sledepus/Development-of-a-Distributed-Synchronized-Camera-System-for-Real-Time-Underwater-Monitoring/Mechanical Assembly - CAD/Hexadome Prototype/Lens_asm.SLDASM

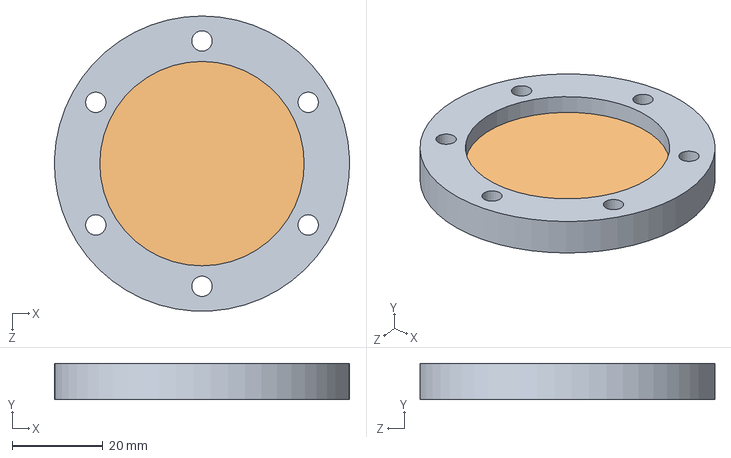
[picture p4: CAD file, 2025-05-22]
Mechanical Assembly - CAD/Hexadome Prototype/Lens_asm.SLDASM
65.0 x 8.00 x 64.9 mm
Lens_glass_45
Lens_cover_simple
