sledepus/Development-of-a-Distributed-Synchronized-Camera-System-for-Real-Time-Underwater-Monitoring/Mechanical Assembly - CAD/Hexadome Prototype/Wide_node_case_asm.SLDASM

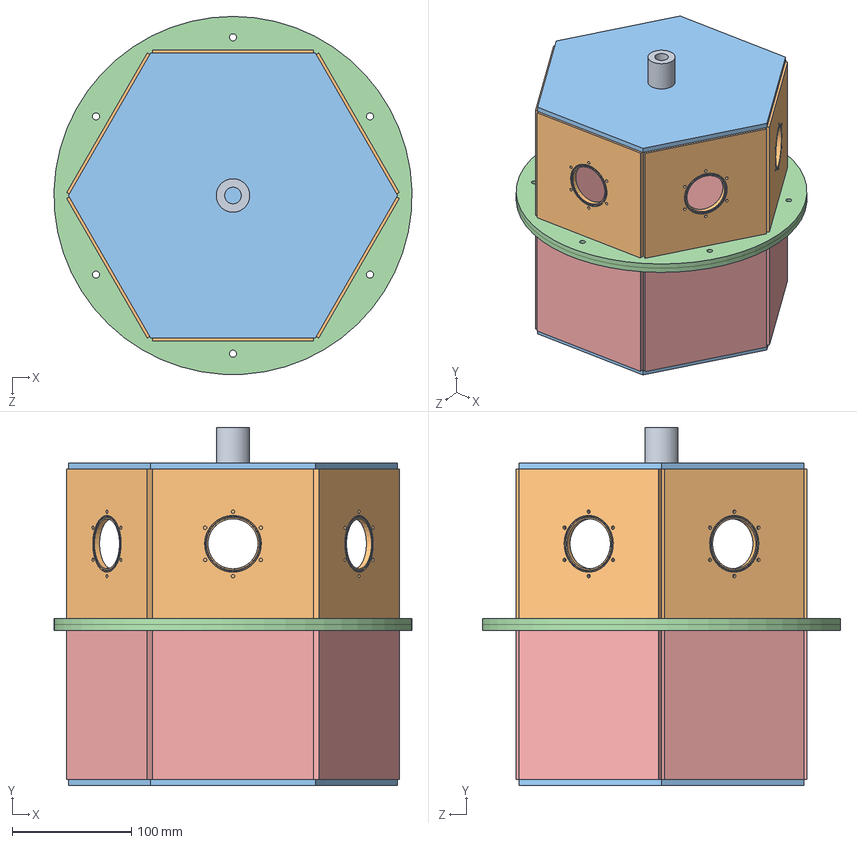
[picture p5: CAD file, 2025-05-22]
Mechanical Assembly - CAD/Hexadome Prototype/Wide_node_case_asm.SLDASM
299.9 x 300.0 x 300.0 mm
Wide_bottom_wall x 6
Wide_flange x 2
Wide_lock x 2
Wide_top_wall x 6
Boss
