sledepus/Development-of-a-Distributed-Synchronized-Camera-System-for-Real-Time-Underwater-Monitoring/Mechanical Assembly - CAD/Hexadome Prototype/Wide_bottom_asm.SLDASM

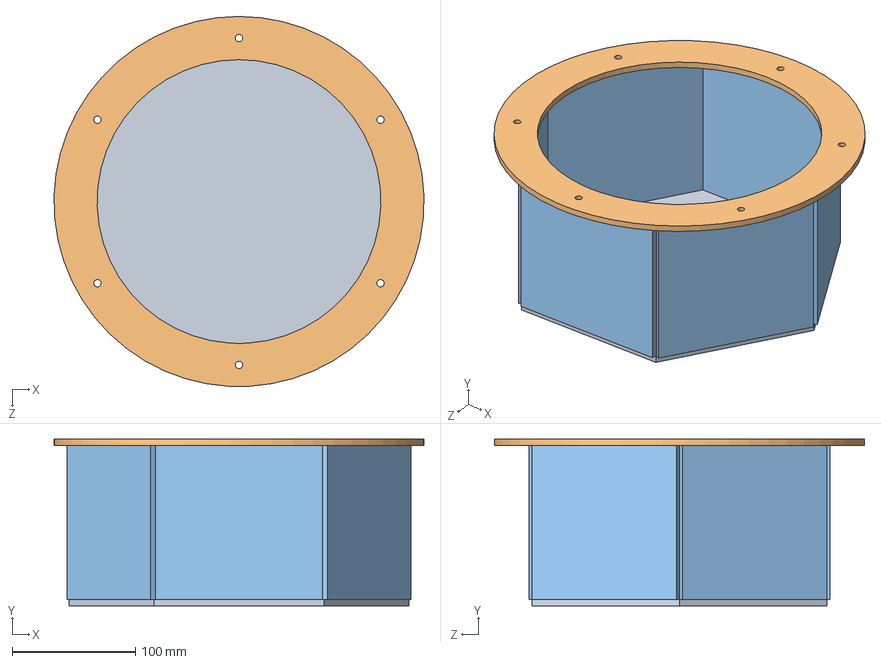
[picture p6: CAD file, 2025-05-22]
Mechanical Assembly - CAD/Hexadome Prototype/Wide_bottom_asm.SLDASM
299.9 x 135.0 x 300.0 mm
Wide_bottom_wall x 6
Wide_flange
Wide_lock
