sledepus/Development-of-a-Distributed-Synchronized-Camera-System-for-Real-Time-Underwater-Monitoring/Mechanical Assembly - CAD/Hexadome Prototype/Jetson_Dummy_Serial_board.SLDPRT

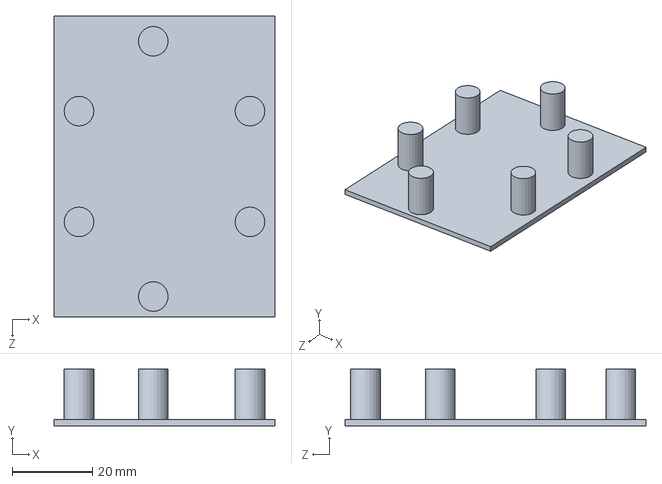
[picture p14: CAD file, 2025-05-22]
Mechanical Assembly - CAD/Hexadome Prototype/Jetson_Dummy_Serial_board.SLDPRT
55.0 x 14.1 x 75.0 mm
