sledepus/Development-of-a-Distributed-Synchronized-Camera-System-for-Real-Time-Underwater-Monitoring/Mechanical Assembly - CAD/Sensor Board/Large_Sensor_PCB_bracket.SLDPRT

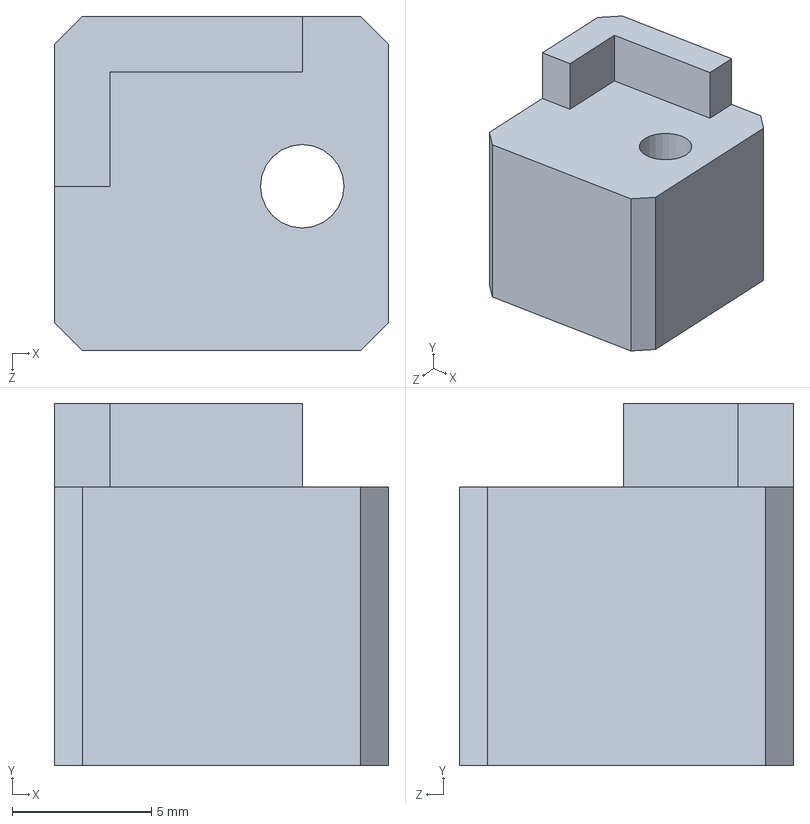
[picture p15: CAD file, 2025-05-22]
Mechanical Assembly - CAD/Sensor Board/Large_Sensor_PCB_bracket.SLDPRT
12.0 x 13.0 x 12.0 mm
