sledepus/Development-of-a-Distributed-Synchronized-Camera-System-for-Real-Time-Underwater-Monitoring/Electronics/Power board/local symbols/EEV-FK2A221M.stp

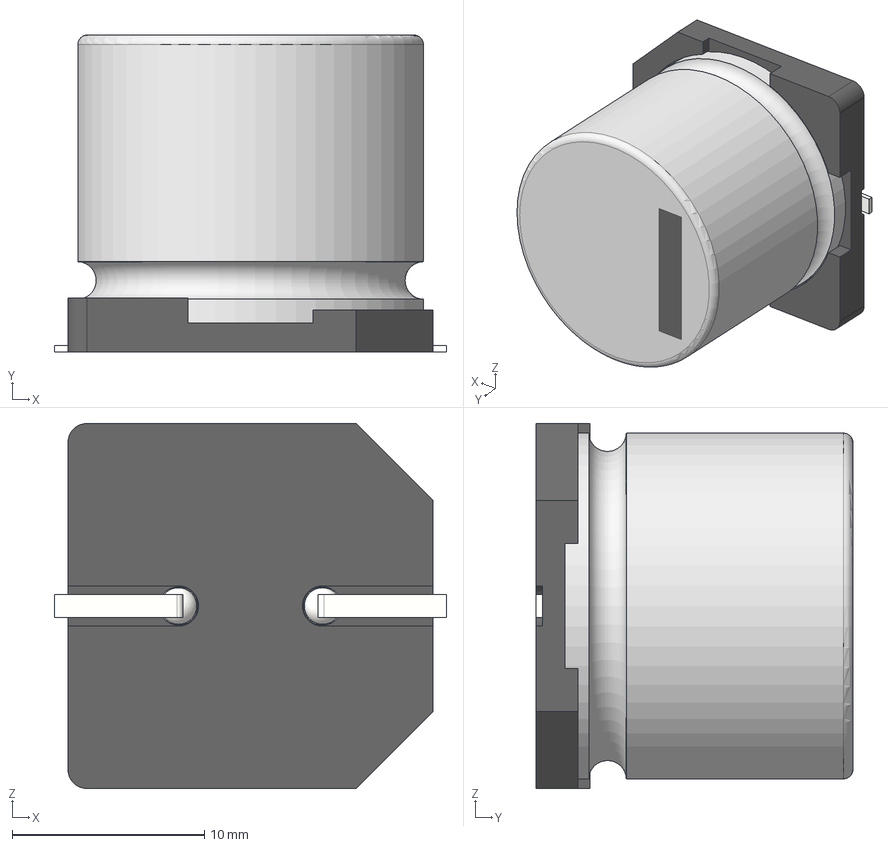
[picture p16: CAD file, 2025-05-22]
Electronics/Power board/local symbols/EEV-FK2A221M.stp
20.4 x 16.5 x 19.0 mm
標準品ケースΦ18x15L SIDE CODE K1 6
標準品座版Φ18 SIZE CODE K16
標準品リード線Φ18 SIZE CODE K1 6 x 2
