sledepus/Development-of-a-Distributed-Synchronized-Camera-System-for-Real-Time-Underwater-Monitoring/Mechanical Assembly - CAD/Final updated design/Bottom_node.SLDPRT

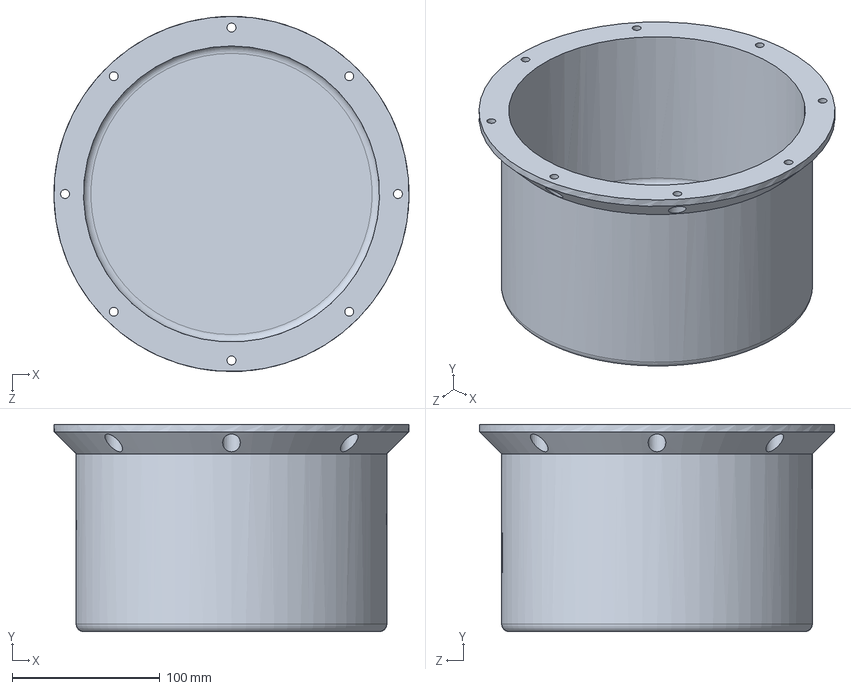
[picture p17: CAD file, 2025-05-22]
Mechanical Assembly - CAD/Final updated design/Bottom_node.SLDPRT
239.9 x 140.0 x 240.0 mm
