sledepus/Development-of-a-Distributed-Synchronized-Camera-System-for-Real-Time-Underwater-Monitoring/Mechanical Assembly - CAD/Final updated design/Hook.SLDPRT

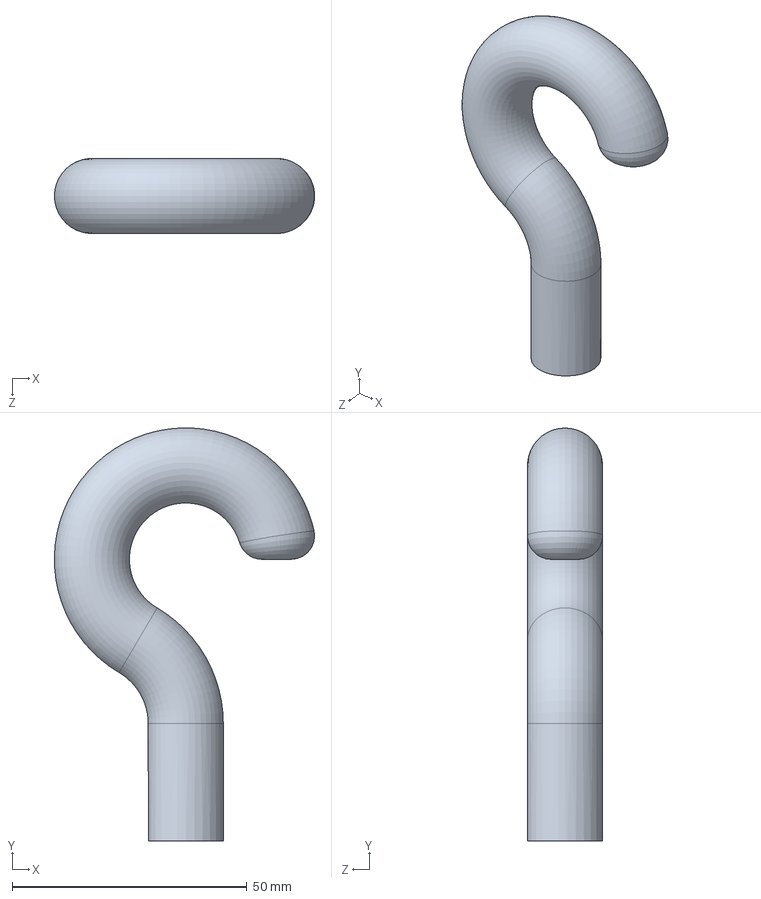
[picture p18: CAD file, 2025-05-22]
Mechanical Assembly - CAD/Final updated design/Hook.SLDPRT
55.4 x 88.0 x 16.0 mm
