sledepus/Development-of-a-Distributed-Synchronized-Camera-System-for-Real-Time-Underwater-Monitoring/Electronics/Power board/local symbols/Download_STP_WE-XHMI-1090 (rev1).stp

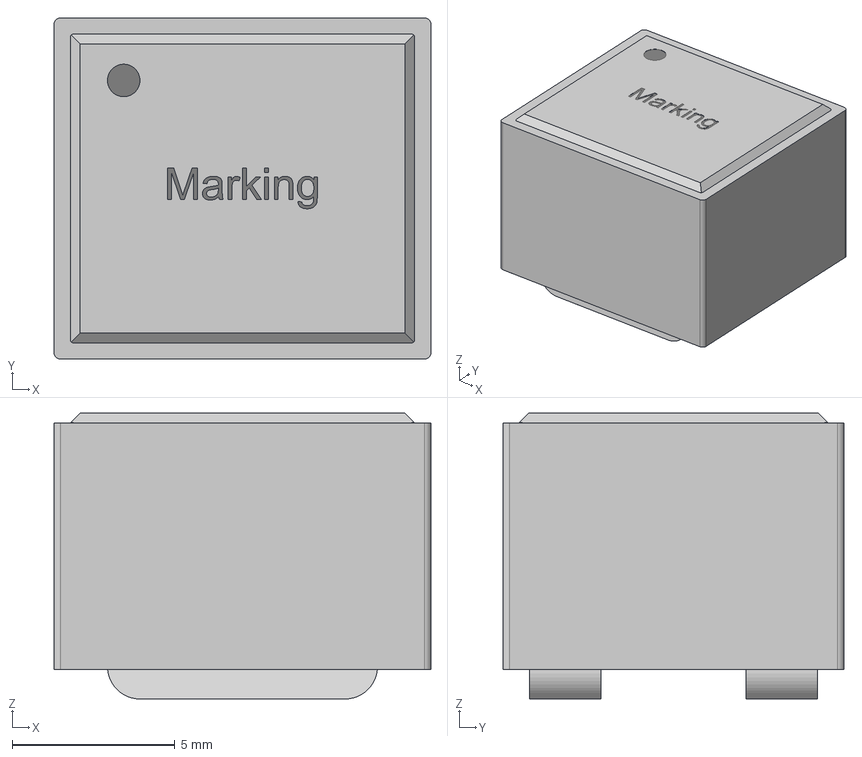
[picture p19: CAD file, 2025-05-22]
Electronics/Power board/local symbols/Download_STP_WE-XHMI-1090 (rev1).stp
11.6 x 10.5 x 8.80 mm
