sledepus/Development-of-a-Distributed-Synchronized-Camera-System-for-Real-Time-Underwater-Monitoring/Mechanical Assembly - CAD/Final updated design/Anchor.SLDPRT

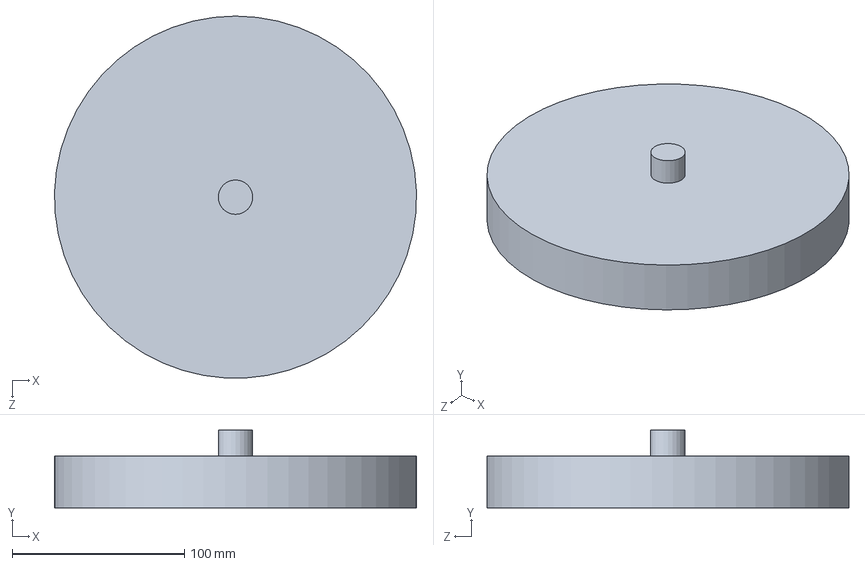
[picture p20: CAD file, 2025-05-22]
Mechanical Assembly - CAD/Final updated design/Anchor.SLDPRT
209.9 x 45.0 x 209.8 mm
