sledepus/Development-of-a-Distributed-Synchronized-Camera-System-for-Real-Time-Underwater-Monitoring/Mechanical Assembly - CAD/Hexadome Prototype/Node_leg_base.SLDPRT

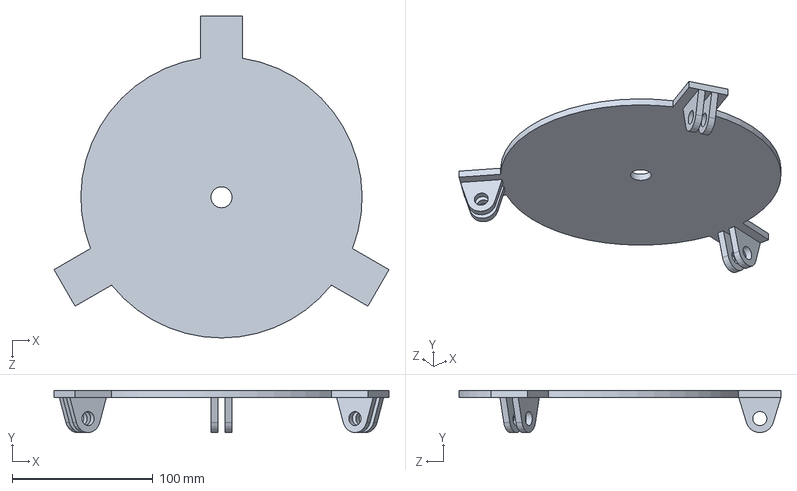
[picture p21: CAD file, 2025-05-22]
Mechanical Assembly - CAD/Hexadome Prototype/Node_leg_base.SLDPRT
238.2 x 30.0 x 228.9 mm
