sledepus/Development-of-a-Distributed-Synchronized-Camera-System-for-Real-Time-Underwater-Monitoring/Electronics/Power board/local symbols/VQFN32_6X6_3EP_PHA_MCH.step

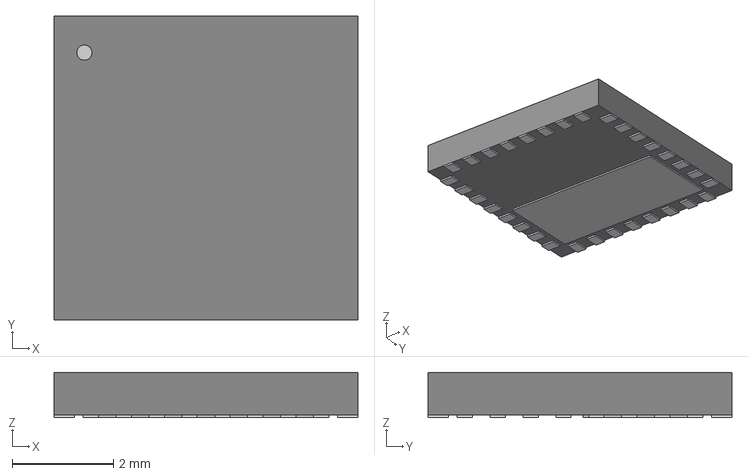
[picture p22: CAD file, 2025-05-22]
Electronics/Power board/local symbols/VQFN32_6X6_3EP_PHA_MCH.step
5.99 x 5.99 x 0.892 mm
