sledepus/Development-of-a-Distributed-Synchronized-Camera-System-for-Real-Time-Underwater-Monitoring/Electronics/Power board/local symbols/20SVPA10M.stp

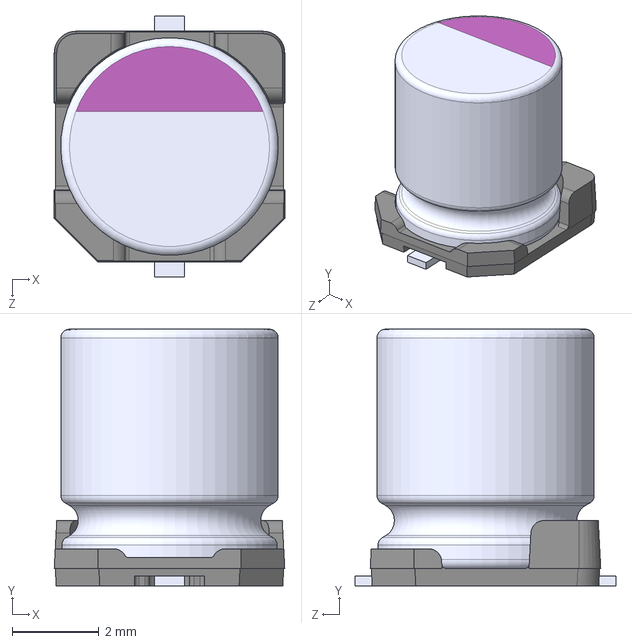
[picture p23: CAD file, 2025-05-22]
Electronics/Power board/local symbols/20SVPA10M.stp
5.30 x 5.90 x 6.00 mm
