sledepus/Development-of-a-Distributed-Synchronized-Camera-System-for-Real-Time-Underwater-Monitoring/Mechanical Assembly - CAD/Final updated design/Optimal_lens.SLDPRT

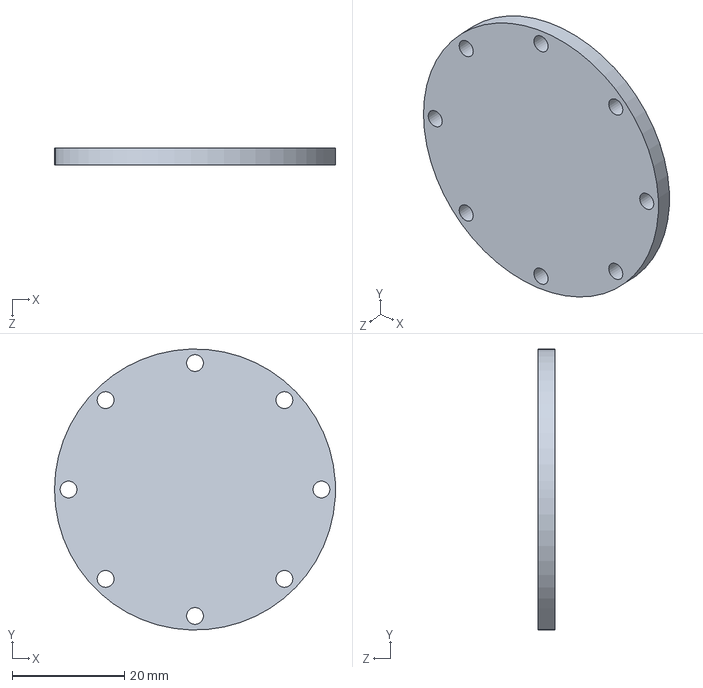
[picture p24: CAD file, 2025-05-22]
Mechanical Assembly - CAD/Final updated design/Optimal_lens.SLDPRT
50.0 x 50.0 x 3.00 mm
