sledepus/Development-of-a-Distributed-Synchronized-Camera-System-for-Real-Time-Underwater-Monitoring/Mechanical Assembly - CAD/Hexadome Prototype/Boss.SLDPRT

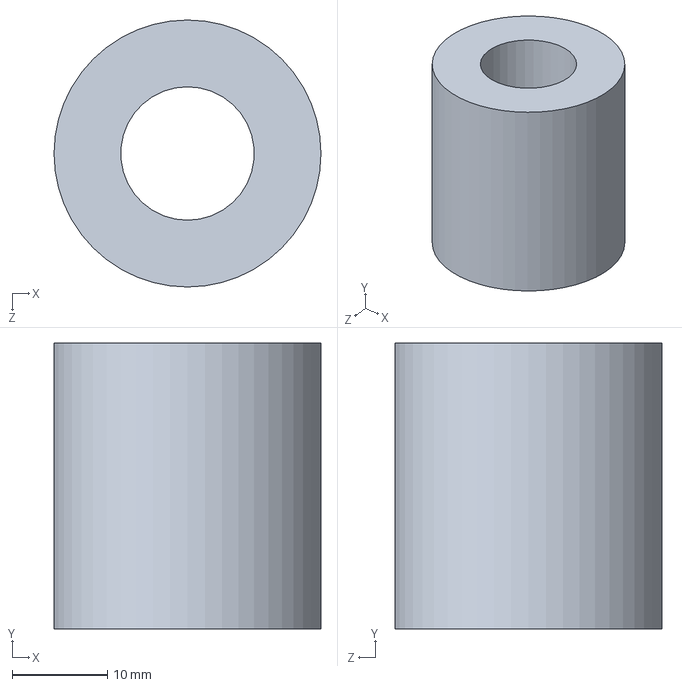
[picture p25: CAD file, 2025-05-22]
Mechanical Assembly - CAD/Hexadome Prototype/Boss.SLDPRT
28.0 x 30.0 x 28.0 mm
