sledepus/Development-of-a-Distributed-Synchronized-Camera-System-for-Real-Time-Underwater-Monitoring/Electronics/Power board/local symbols/SS-60000-008.step

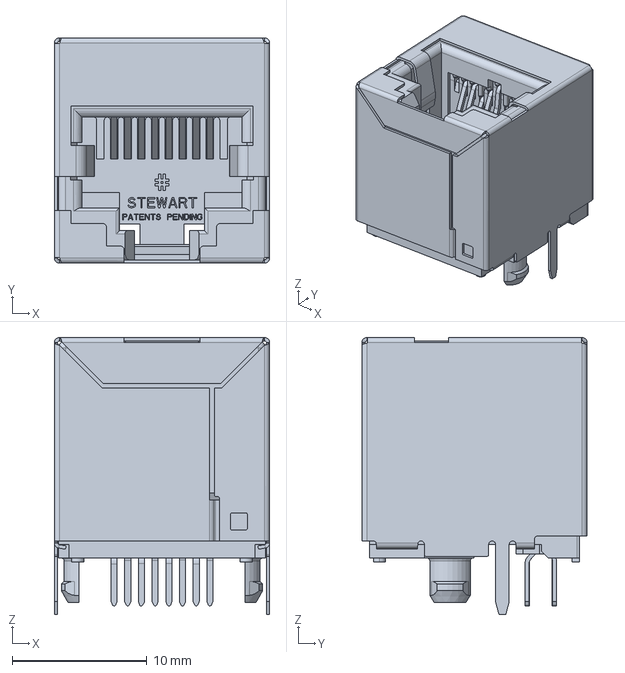
[picture p26: CAD file, 2025-05-22]
Electronics/Power board/local symbols/SS-60000-008.step
16.0 x 16.7 x 20.6 mm
