sledepus/Development-of-a-Distributed-Synchronized-Camera-System-for-Real-Time-Underwater-Monitoring/Mechanical Assembly - CAD/Hexadome Prototype/Camera_lock_v2.SLDPRT

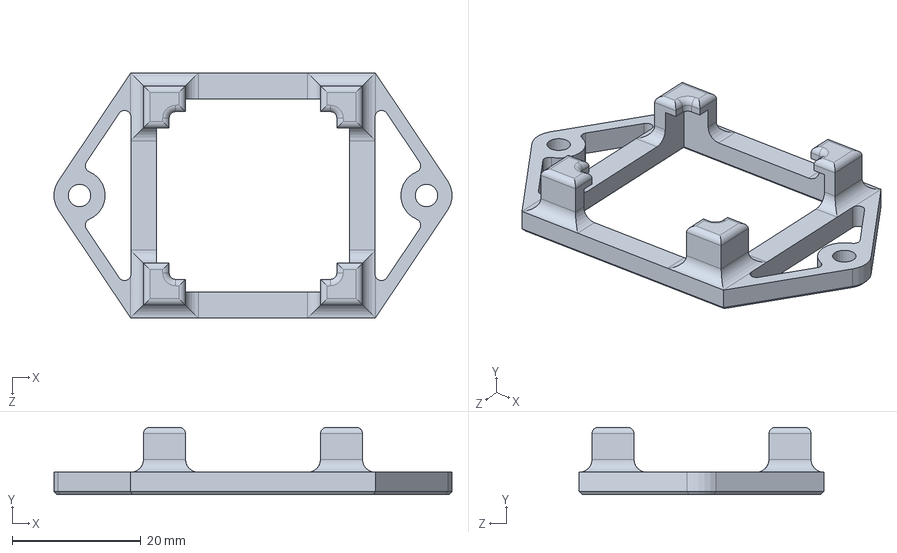
[picture p27: CAD file, 2025-05-22]
Mechanical Assembly - CAD/Hexadome Prototype/Camera_lock_v2.SLDPRT
61.9 x 10.5 x 38.1 mm
