sledepus/Development-of-a-Distributed-Synchronized-Camera-System-for-Real-Time-Underwater-Monitoring/Mechanical Assembly - CAD/Hexadome Prototype/Wide_flange.SLDPRT

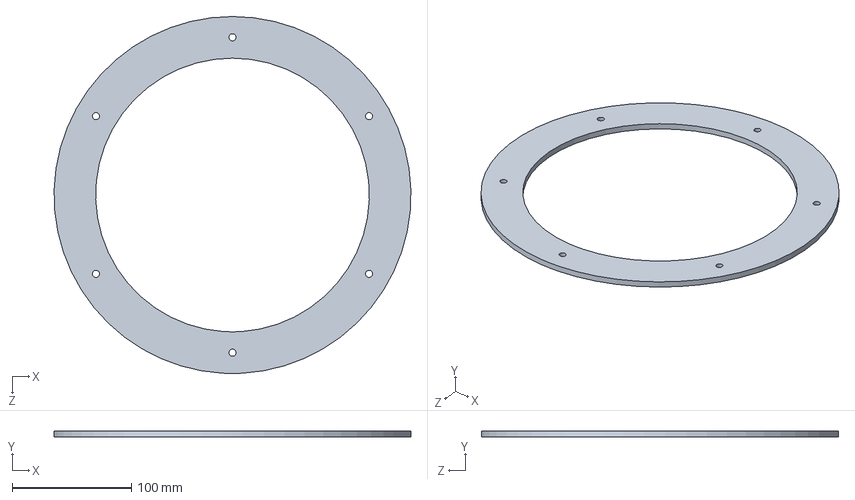
[picture p28: CAD file, 2025-05-22]
Mechanical Assembly - CAD/Hexadome Prototype/Wide_flange.SLDPRT
299.9 x 5.00 x 300.0 mm
