sledepus/Development-of-a-Distributed-Synchronized-Camera-System-for-Real-Time-Underwater-Monitoring/Mechanical Assembly - CAD/Hexadome Prototype/Node_leg_leg.SLDPRT

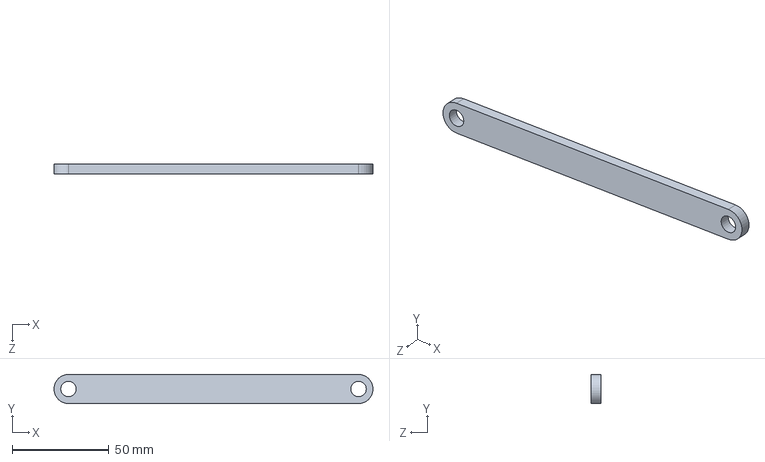
[picture p29: CAD file, 2025-05-22]
Mechanical Assembly - CAD/Hexadome Prototype/Node_leg_leg.SLDPRT
164.9 x 15.0 x 5.00 mm
