sledepus/Development-of-a-Distributed-Synchronized-Camera-System-for-Real-Time-Underwater-Monitoring/Electronics/Power board/local symbols/WE-RJ45_7499511420.step

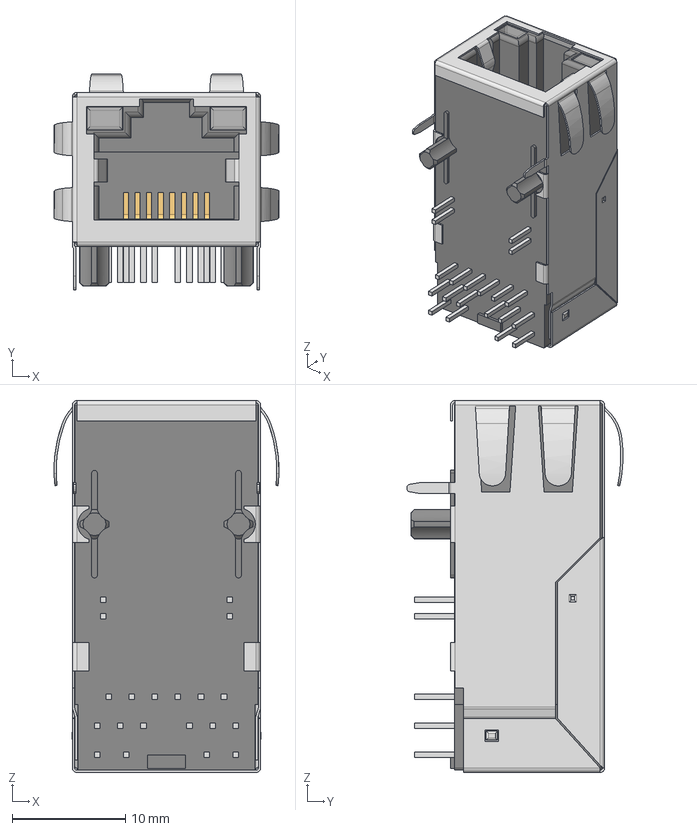
[picture p30: CAD file, 2025-05-22]
Electronics/Power board/local symbols/WE-RJ45_7499511420.step
19.8 x 19.0 x 32.8 mm
Shielding
Base
