sledepus/Development-of-a-Distributed-Synchronized-Camera-System-for-Real-Time-Underwater-Monitoring/Electronics/Power board/local symbols/LT4293IMS_PBF.step

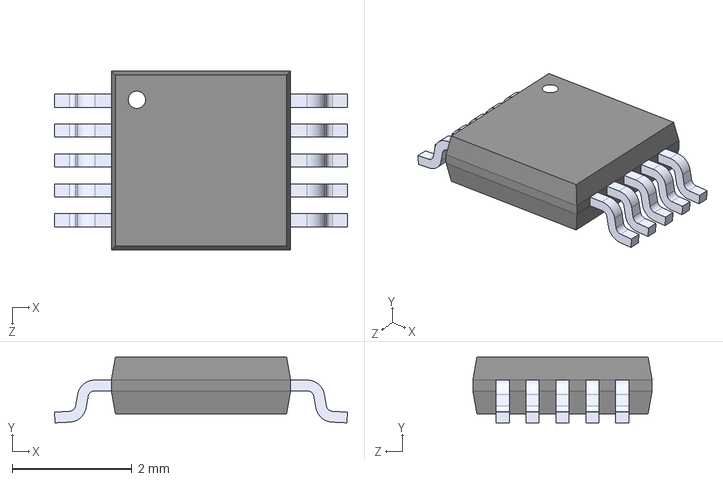
[picture p31: CAD file, 2025-05-22]
Electronics/Power board/local symbols/LT4293IMS_PBF.step
4.90 x 1.10 x 3.00 mm
