sledepus/Development-of-a-Distributed-Synchronized-Camera-System-for-Real-Time-Underwater-Monitoring/Electronics/Power board/local symbols/SS-60300-080.step

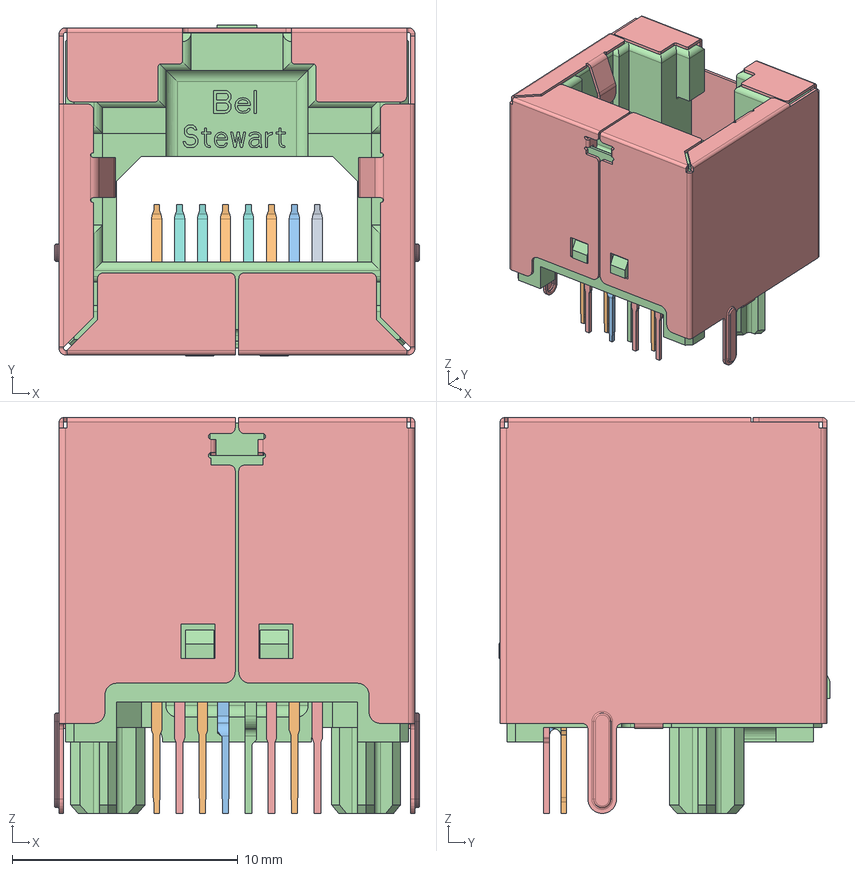
[picture p32: CAD file, 2025-05-22]
Electronics/Power board/local symbols/SS-60300-080.step
16.2 x 14.7 x 17.5 mm
3206M0010-07
5303M0201-06
5303M0201-05
3200M0013-26
0048M00E1-14
