sledepus/Development-of-a-Distributed-Synchronized-Camera-System-for-Real-Time-Underwater-Monitoring/Mechanical Assembly - CAD/Hexadome Prototype/Jetson_Dummy_PCB.SLDPRT

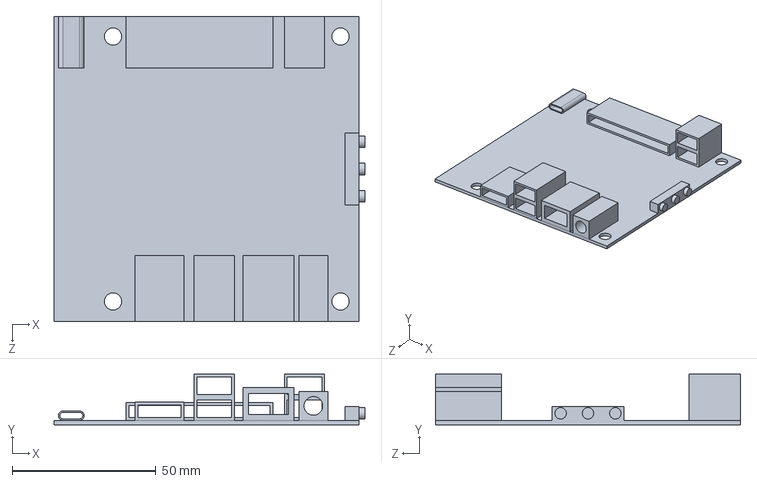
[picture p33: CAD file, 2025-05-22]
Mechanical Assembly - CAD/Hexadome Prototype/Jetson_Dummy_PCB.SLDPRT
108.0 x 17.6 x 106.0 mm
