sledepus/Development-of-a-Distributed-Synchronized-Camera-System-for-Real-Time-Underwater-Monitoring/Mechanical Assembly - CAD/Hexadome Prototype/O_ring.SLDPRT

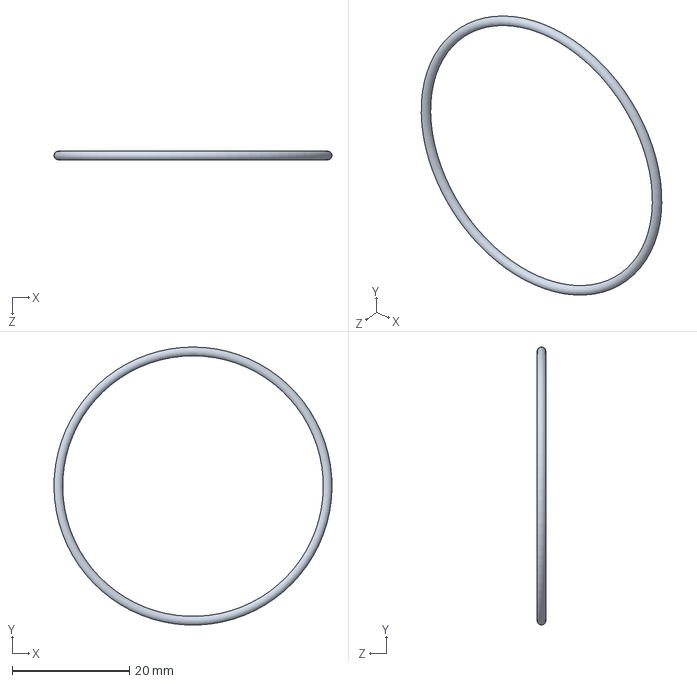
[picture p34: CAD file, 2025-05-22]
Mechanical Assembly - CAD/Hexadome Prototype/O_ring.SLDPRT
47.5 x 47.5 x 1.50 mm
