sledepus/Development-of-a-Distributed-Synchronized-Camera-System-for-Real-Time-Underwater-Monitoring/Electronics/Power board/local symbols/EEU-FS2A221B.stp

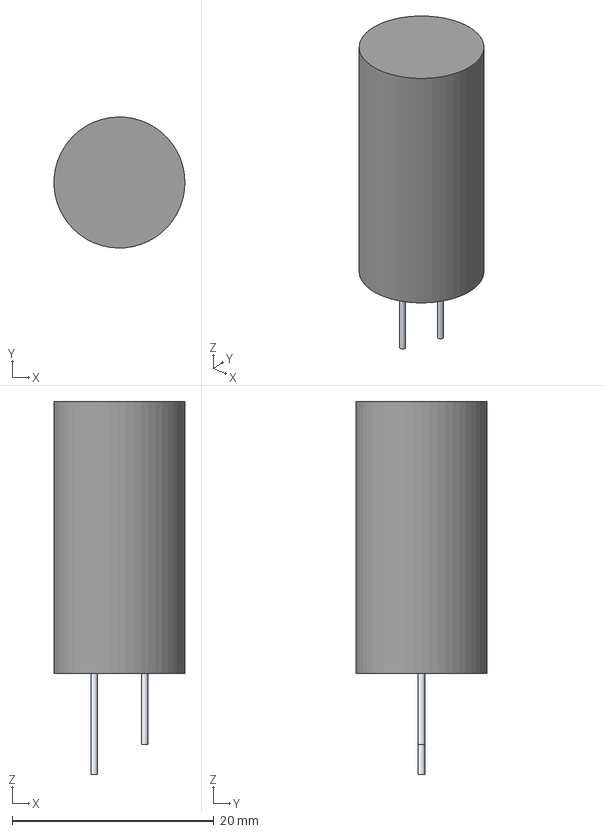
[picture p35: CAD file, 2025-05-22]
Electronics/Power board/local symbols/EEU-FS2A221B.stp
13.0 x 13.0 x 37.0 mm
SimpleBody
Pin1
Pin2
