sledepus/Development-of-a-Distributed-Synchronized-Camera-System-for-Real-Time-Underwater-Monitoring/Mechanical Assembly - CAD/Hexadome Prototype/Bulkhead.SLDPRT

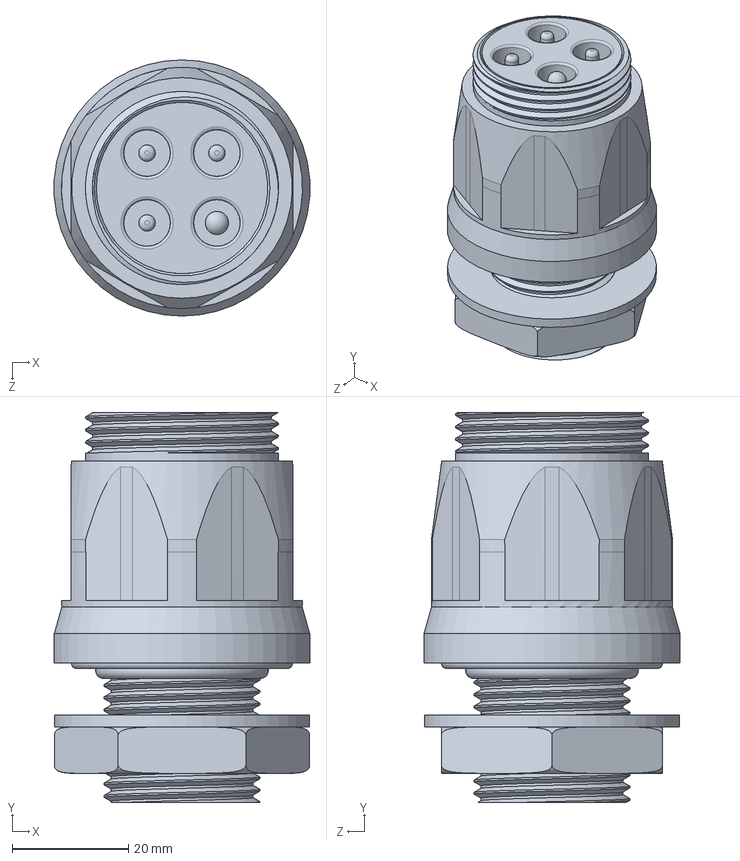
[picture p36: CAD file, 2025-05-22]
Mechanical Assembly - CAD/Hexadome Prototype/Bulkhead.SLDPRT
43.9 x 67.0 x 44.0 mm
