sledepus/Development-of-a-Distributed-Synchronized-Camera-System-for-Real-Time-Underwater-Monitoring/Mechanical Assembly - CAD/Hexadome Prototype/Lens_glass_45.SLDPRT

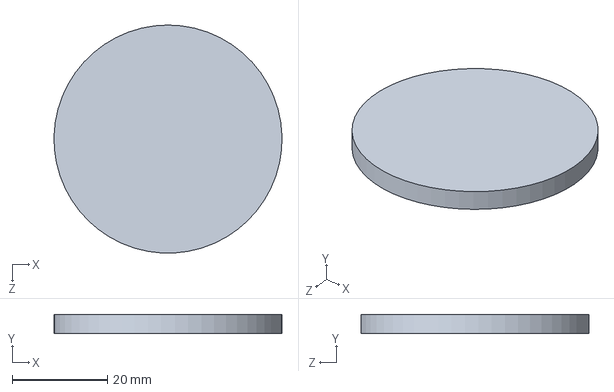
[picture p37: CAD file, 2025-05-22]
Mechanical Assembly - CAD/Hexadome Prototype/Lens_glass_45.SLDPRT
48.0 x 4.00 x 48.0 mm
