sledepus/Development-of-a-Distributed-Synchronized-Camera-System-for-Real-Time-Underwater-Monitoring/Mechanical Assembly - CAD/Hexadome Prototype/Wide_lock.SLDPRT

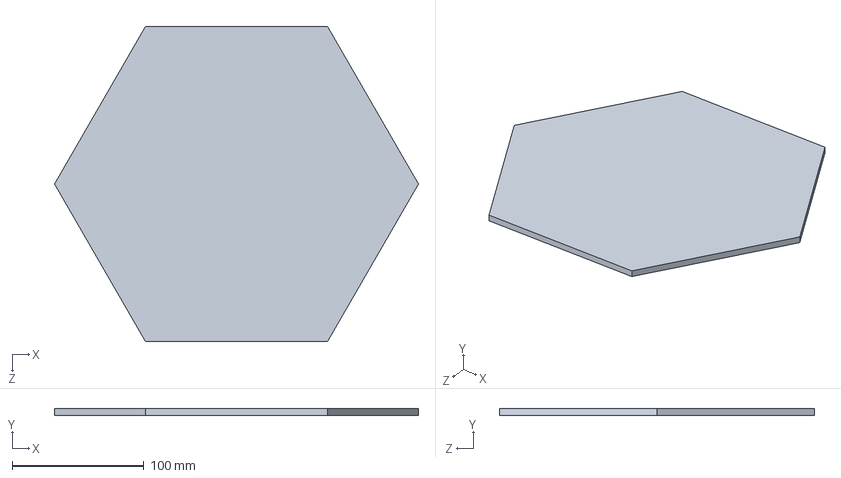
[picture p39: CAD file, 2025-05-22]
Mechanical Assembly - CAD/Hexadome Prototype/Wide_lock.SLDPRT
275.8 x 5.00 x 238.8 mm
