sledepus/Development-of-a-Distributed-Synchronized-Camera-System-for-Real-Time-Underwater-Monitoring/Mechanical Assembly - CAD/Hexadome Prototype/Wide_Gasket.SLDPRT

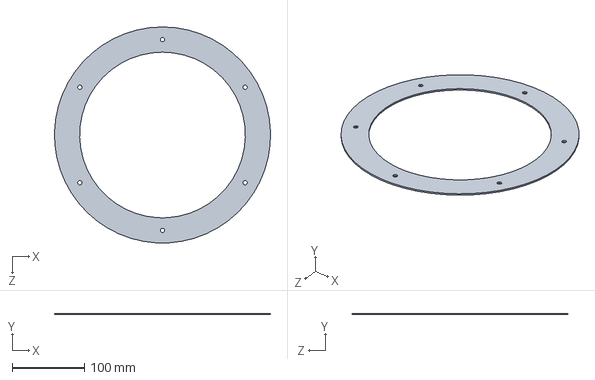
[picture p41: CAD file, 2025-05-22]
Mechanical Assembly - CAD/Hexadome Prototype/Wide_Gasket.SLDPRT
299.9 x 2.00 x 300.0 mm
