sledepus/Development-of-a-Distributed-Synchronized-Camera-System-for-Real-Time-Underwater-Monitoring/Mechanical Assembly - CAD/Hexadome Prototype/Camera_bracket_v3_45mm.SLDPRT

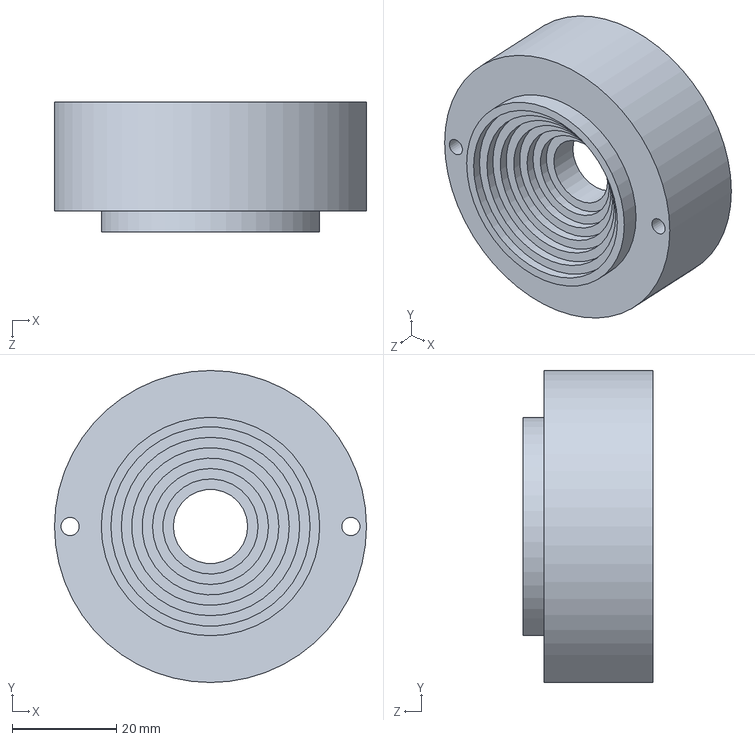
[picture p42: CAD file, 2025-05-22]
Mechanical Assembly - CAD/Hexadome Prototype/Camera_bracket_v3_45mm.SLDPRT
60.0 x 60.0 x 25.0 mm
