sledepus/Development-of-a-Distributed-Synchronized-Camera-System-for-Real-Time-Underwater-Monitoring/Mechanical Assembly - CAD/Hexadome Prototype/Wide_bottom_wall.SLDPRT

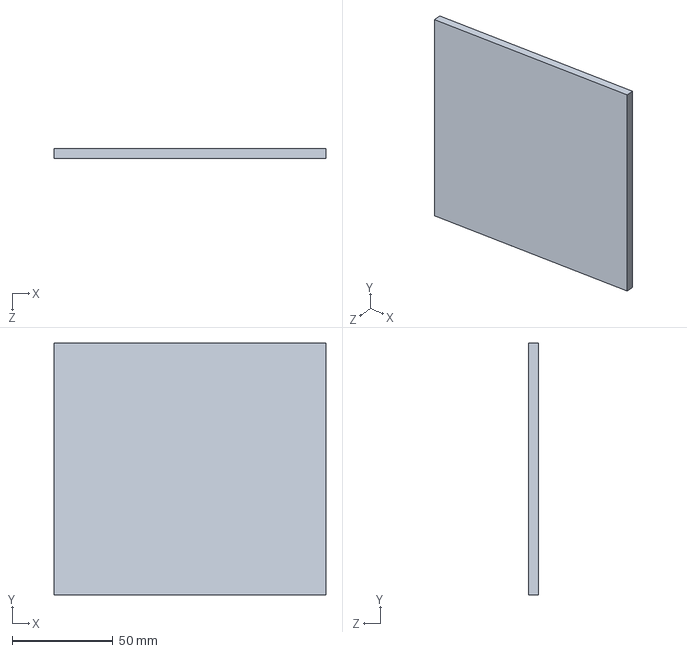
[picture p43: CAD file, 2025-05-22]
Mechanical Assembly - CAD/Hexadome Prototype/Wide_bottom_wall.SLDPRT
135.0 x 125.0 x 5.00 mm
